Pronoe/DUAL_TIC_LINKY_ESPHOME_HASS/Electronic definition/Pictures/20240217_083828.jpg

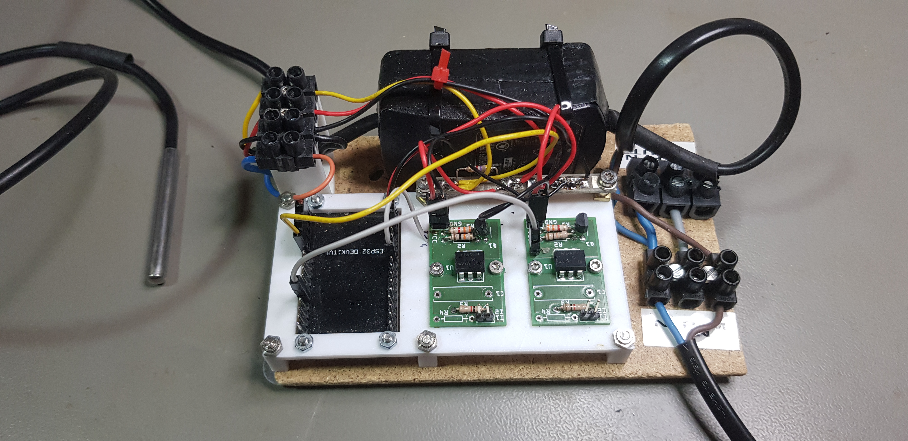
Electronic definition/Pictures/20240217_083828.jpg
